lajos/Tantillus/Laser cut case/Panels - 0.25 inch stock/joint/right_b.dxf

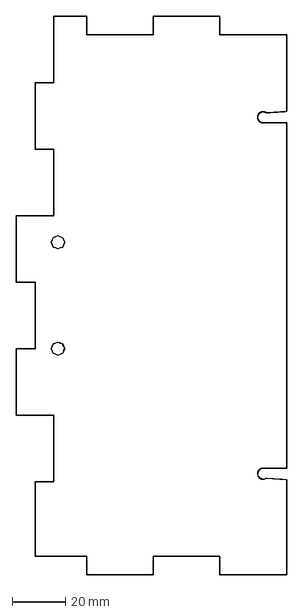
[picture p15: CAD file, 2013-06-04]
Laser cut case/Panels - 0.25 inch stock/joint/right_b.dxf
101.5 x 209.8 mm
