lajos/Tantillus/Laser cut case/Panels - 0.25 inch stock/one piece/front.dxf

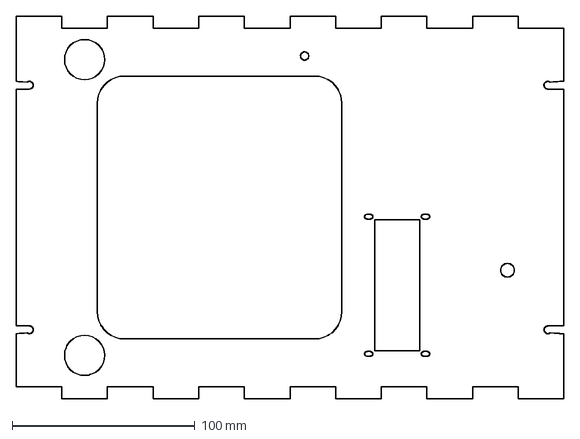
[picture p16: CAD file, 2013-06-04]
Laser cut case/Panels - 0.25 inch stock/one piece/front.dxf
300.0 x 209.8 mm
