lajos/Tantillus/Oilite + Metal Hotend Parts/LED_holder.stl

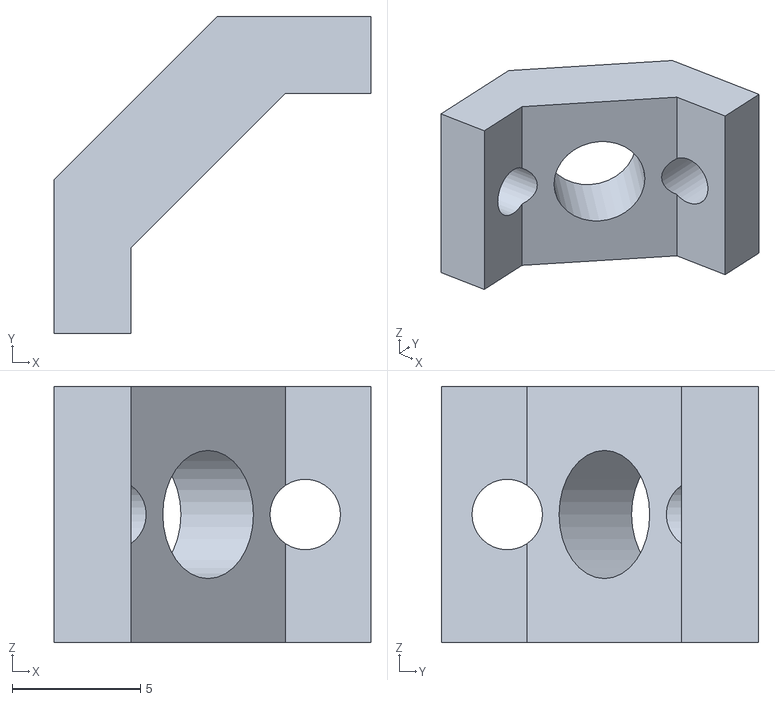
[picture p17: CAD file, 2019-10-04]
Oilite + Metal Hotend Parts/LED_holder.stl
12.4 x 12.4 x 10.0
