lajos/Tantillus/Axis/Oilite/carriage_oilite_bottom.stl

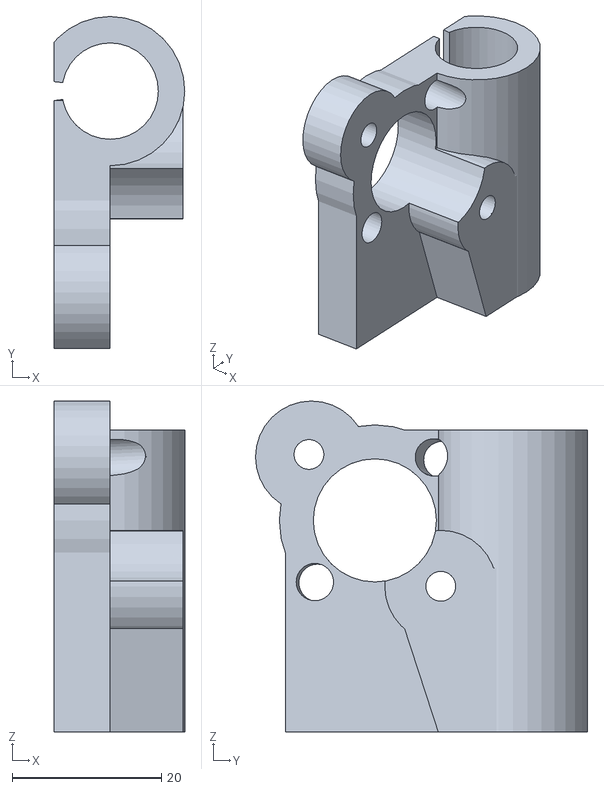
[picture p18: CAD file, 2013-06-04]
Axis/Oilite/carriage_oilite_bottom.stl
17.5 x 44.5 x 44.4
