lajos/Tantillus/Extras/50mm_fanmount_(LC)_0.25_inch_stock.stl

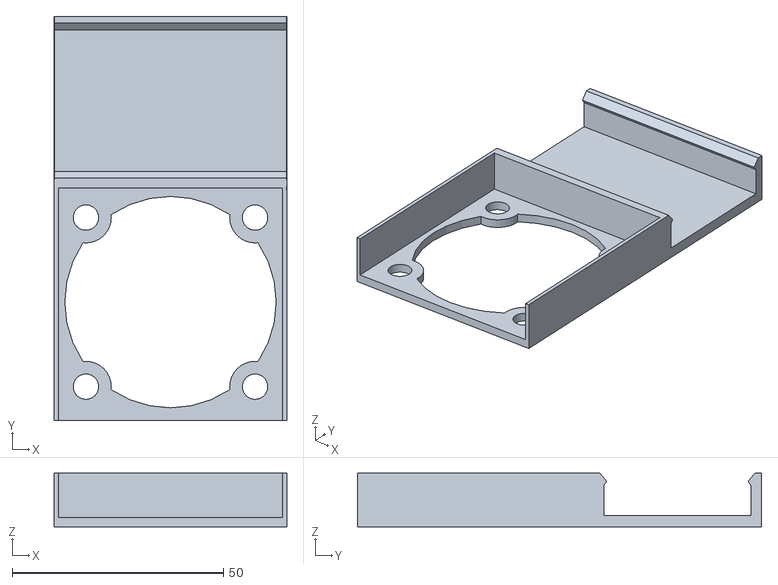
[picture p19: CAD file, 2013-06-04]
Extras/50mm_fanmount_(LC)_0.25_inch_stock.stl
55.0 x 95.6 x 12.7
