lajos/Tantillus/Gears/Spur gears/upper_gear_set.dxf

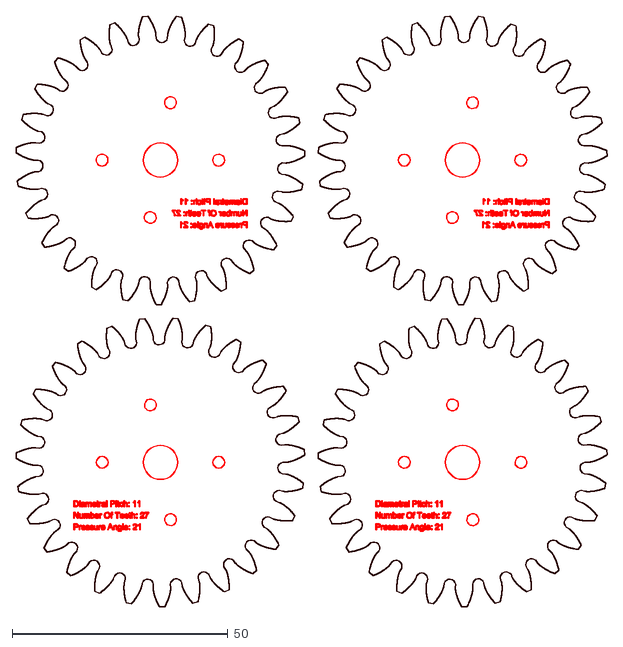
[picture p20: CAD file, 2013-06-05]
Gears/Spur gears/upper_gear_set.dxf
136.9 x 136.8
