lajos/Tantillus/Laser cut case/Corners - 0.25 inch stock/with tabs/corner_top_rear_right.stl

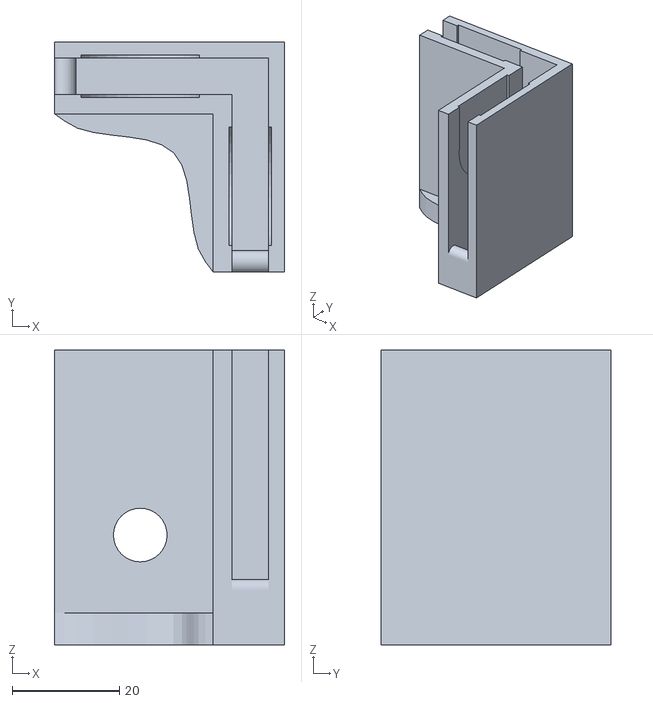
[picture p21: CAD file, 2013-06-04]
Laser cut case/Corners - 0.25 inch stock/with tabs/corner_top_rear_right.stl
42.9 x 42.9 x 55.0
