lajos/Tantillus/Laser cut case/Panels - 0.25 inch stock/joint/right_a.dxf

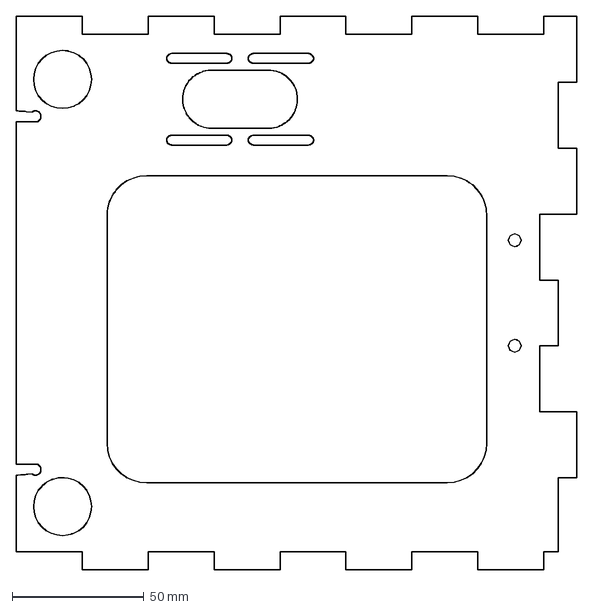
[picture p22: CAD file, 2013-06-04]
Laser cut case/Panels - 0.25 inch stock/joint/right_a.dxf
212.5 x 209.8 mm
