lajos/Tantillus/Oilite + Metal Hotend Parts/xy_slider_b.stl

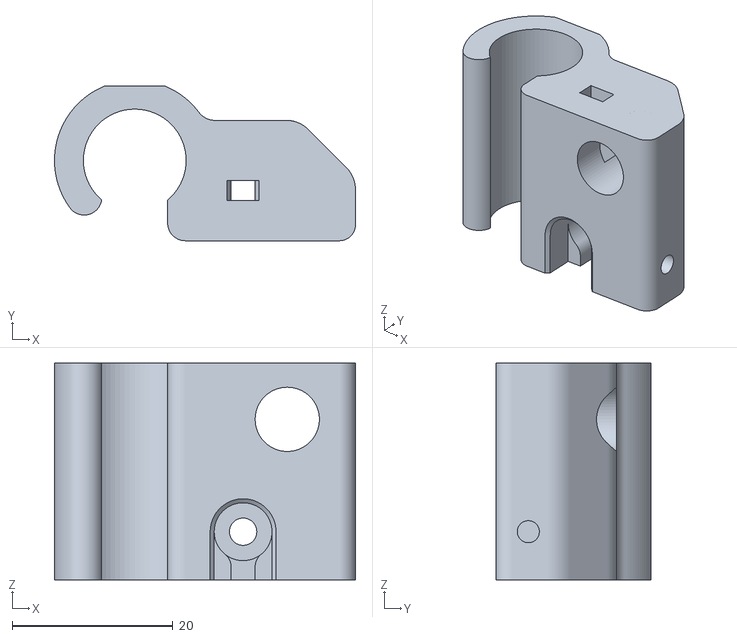
[picture p24: CAD file, 2019-10-03]
Oilite + Metal Hotend Parts/xy_slider_b.stl
37.5 x 19.3 x 27.0
