lajos/Tantillus/Gears/Spur gears/motor_gear.dxf

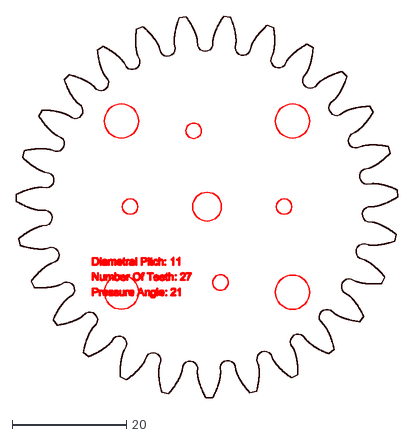
[picture p25: CAD file, 2013-06-05]
Gears/Spur gears/motor_gear.dxf
66.9 x 66.8
