lajos/Tantillus/Laser cut case/Panels - 0.25 inch stock/joint/left_b.dxf

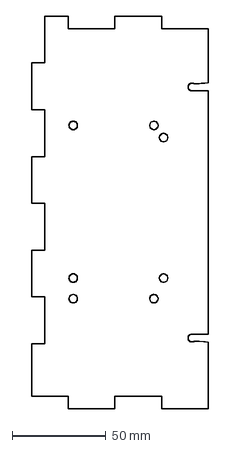
[picture p26: CAD file, 2013-06-04]
Laser cut case/Panels - 0.25 inch stock/joint/left_b.dxf
94.5 x 209.8 mm
