lajos/Tantillus/Oilite + Metal Hotend Parts/spacer_m3_2.stl

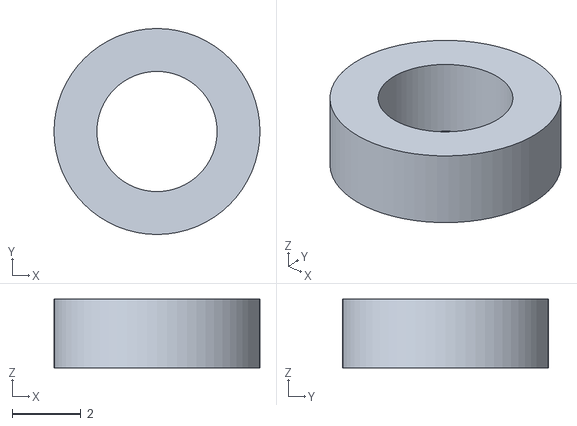
[picture p27: CAD file, 2019-10-03]
Oilite + Metal Hotend Parts/spacer_m3_2.stl
6.00 x 6.00 x 2.00
