lajos/Tantillus/Laser cut case/Panels - 0.25 inch stock/joint/back_a.dxf

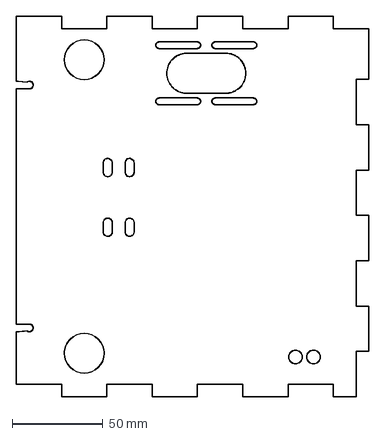
[picture p29: CAD file, 2013-06-04]
Laser cut case/Panels - 0.25 inch stock/joint/back_a.dxf
194.5 x 209.8 mm
