lajos/Tantillus/Oilite + Metal Hotend Parts/spacer_m3_3.stl

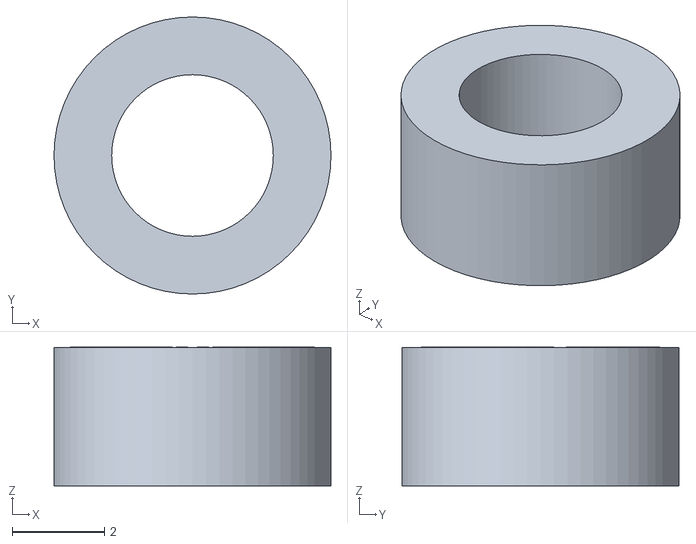
[picture p30: CAD file, 2019-10-03]
Oilite + Metal Hotend Parts/spacer_m3_3.stl
6.00 x 6.00 x 3.00
