lajos/Tantillus/Laser cut case/Panels - 0.25 inch stock/joint/back_b.dxf

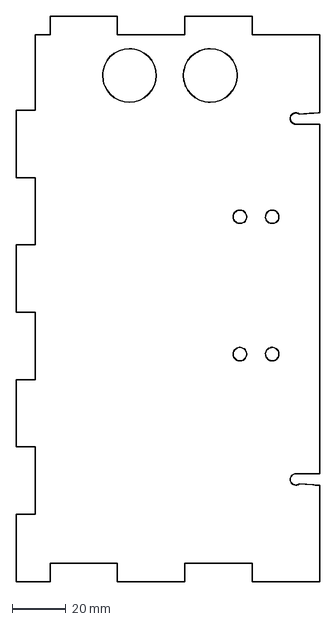
[picture p31: CAD file, 2013-06-04]
Laser cut case/Panels - 0.25 inch stock/joint/back_b.dxf
112.5 x 209.8 mm
