lajos/Tantillus/Oilite + Metal Hotend Parts/z_arm.stl

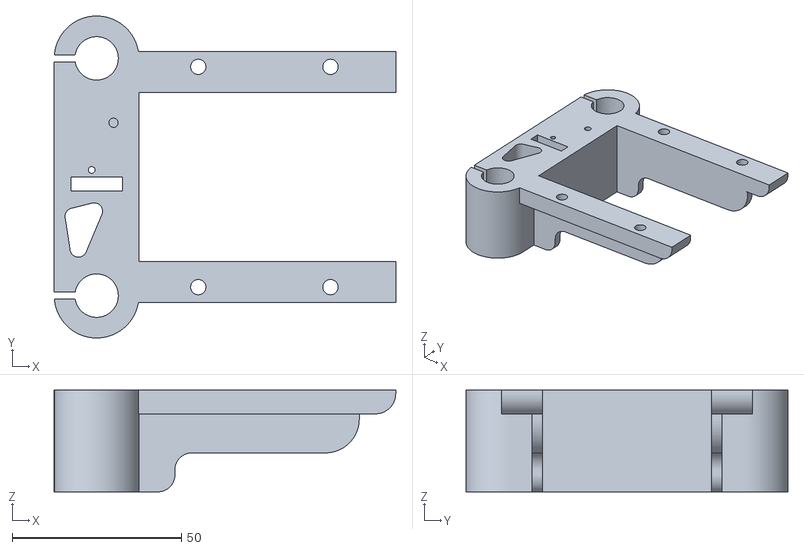
[picture p32: CAD file, 2019-10-03]
Oilite + Metal Hotend Parts/z_arm.stl
100.8 x 95.0 x 30.0
