lajos/Tantillus/Laser cut case/Panels - 0.25 inch stock/joint/front_a.dxf

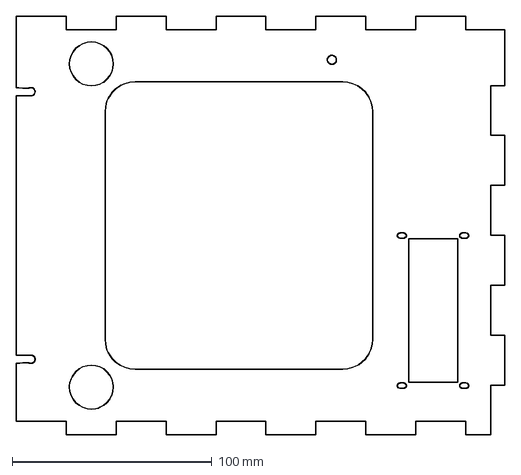
[picture p33: CAD file, 2013-06-04]
Laser cut case/Panels - 0.25 inch stock/joint/front_a.dxf
244.5 x 209.8 mm
