lajos/Tantillus/Laser cut case/Panels - 0.25 inch stock/joint/front_b.dxf

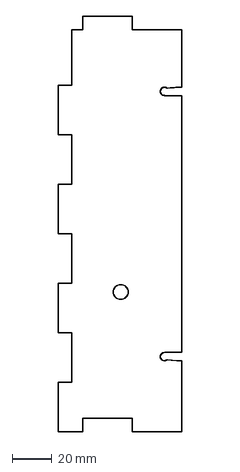
[picture p35: CAD file, 2013-06-04]
Laser cut case/Panels - 0.25 inch stock/joint/front_b.dxf
62.5 x 209.8 mm
