lajos/Tantillus/Oilite + Metal Hotend Parts/z_home_base.stl

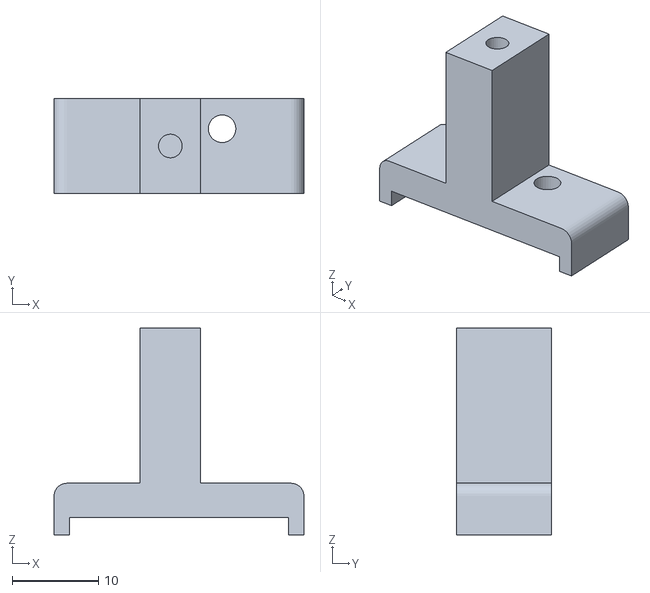
[picture p36: CAD file, 2019-10-03]
Oilite + Metal Hotend Parts/z_home_base.stl
29.0 x 11.0 x 24.0
