lajos/Tantillus/Gears/Spur gears/upper_gear_half.dxf

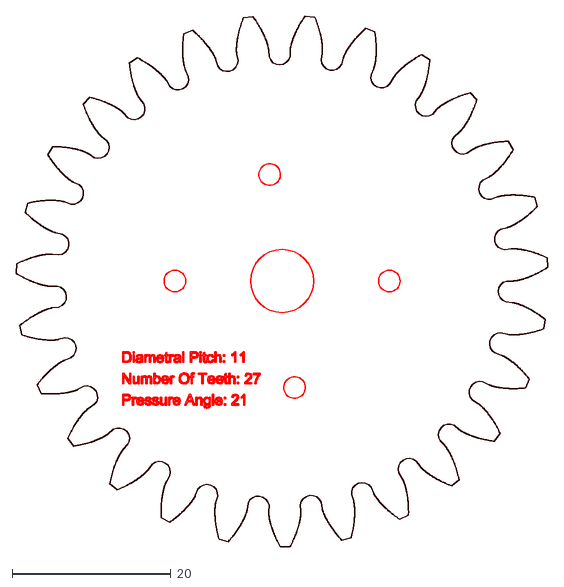
[picture p37: CAD file, 2013-06-04]
Gears/Spur gears/upper_gear_half.dxf
66.9 x 66.8
