lajos/Tantillus/Oilite + Metal Hotend Parts/spacer_m3_5.stl

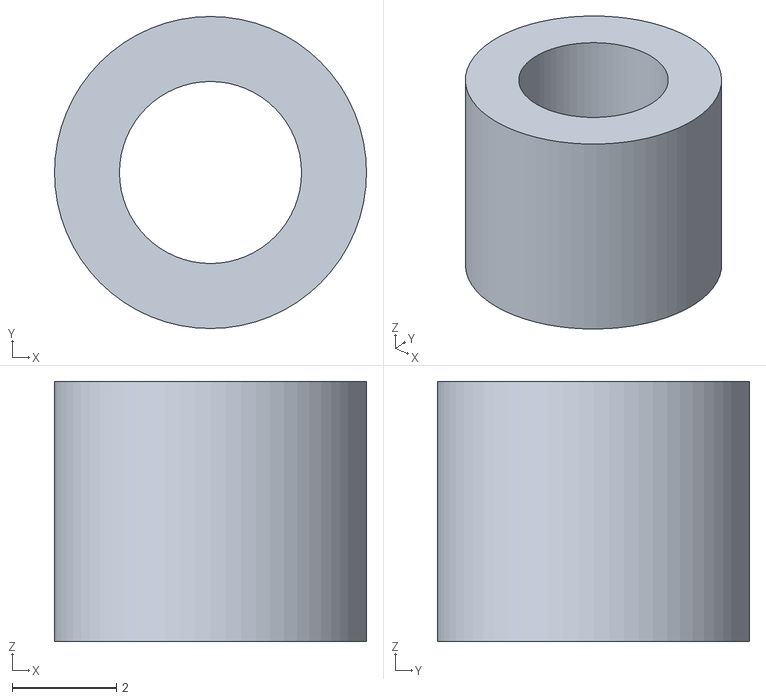
[picture p38: CAD file, 2019-10-03]
Oilite + Metal Hotend Parts/spacer_m3_5.stl
6.00 x 6.00 x 5.00
