lajos/Tantillus/Oilite + Metal Hotend Parts/fan_mount_lower.stl

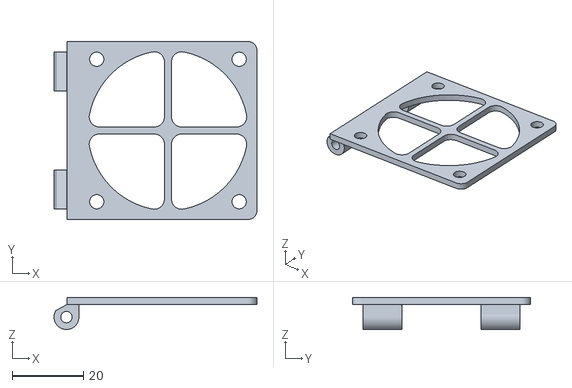
[picture p39: CAD file, 2019-10-03]
Oilite + Metal Hotend Parts/fan_mount_lower.stl
57.0 x 50.0 x 9.01
