lajos/Tantillus/Oilite + Metal Hotend Parts/z_upper.stl

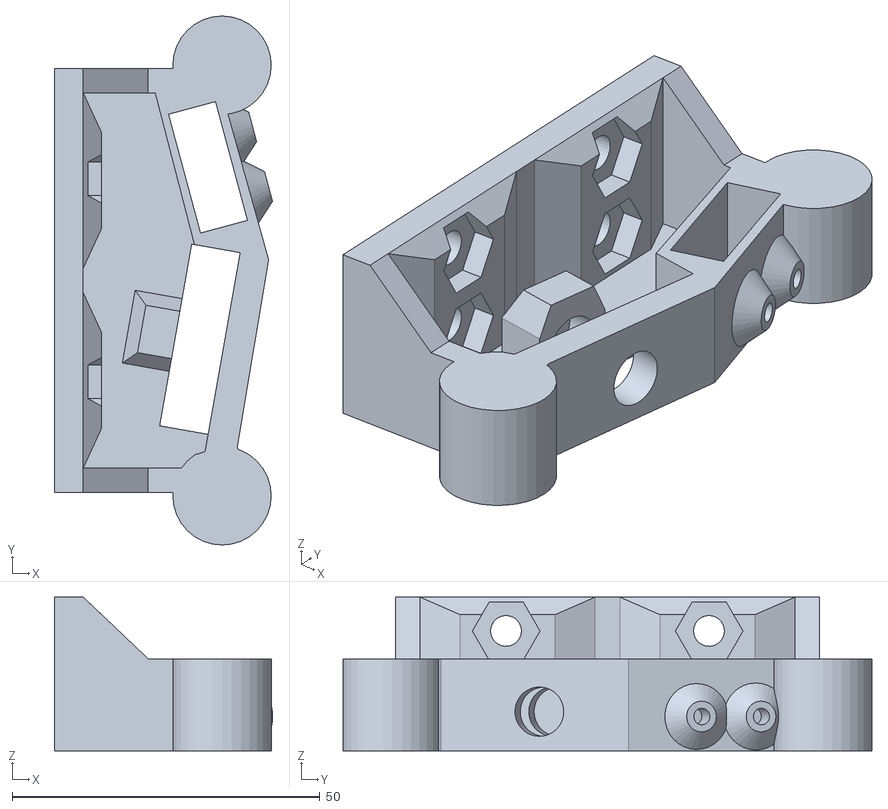
[picture p40: CAD file, 2019-10-03]
Oilite + Metal Hotend Parts/z_upper.stl
35.5 x 86.0 x 25.0
