lajos/Tantillus/Oilite + Metal Hotend Parts/corner_top_rear_left.stl

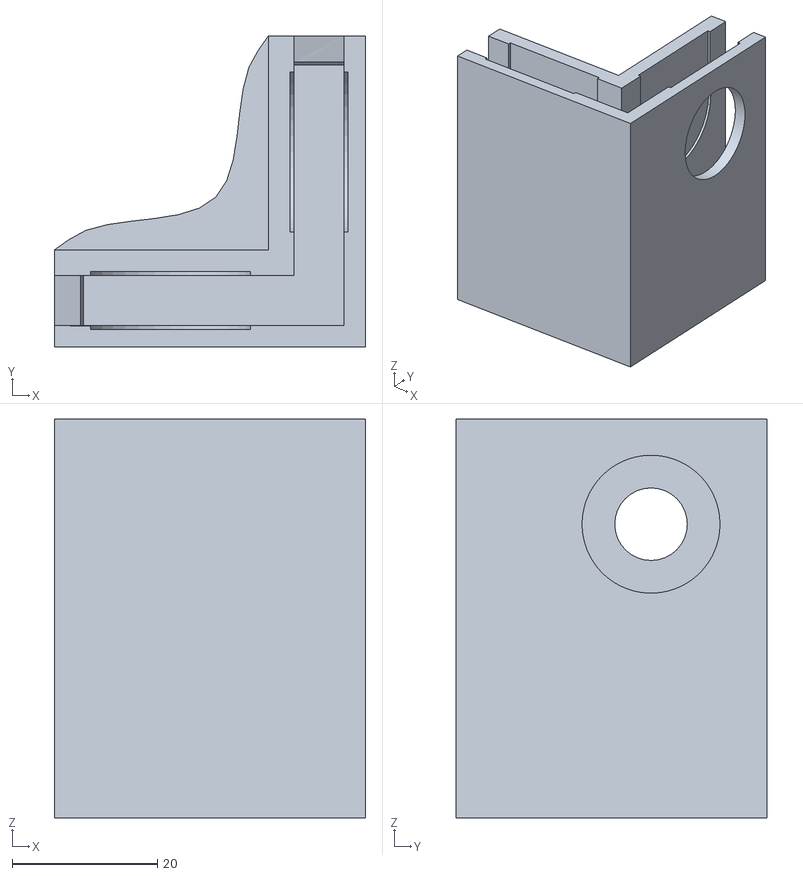
[picture p41: CAD file, 2019-10-03]
Oilite + Metal Hotend Parts/corner_top_rear_left.stl
42.9 x 42.9 x 55.0
