lajos/Tantillus/Oilite + Metal Hotend Parts/z_spacer_short.stl

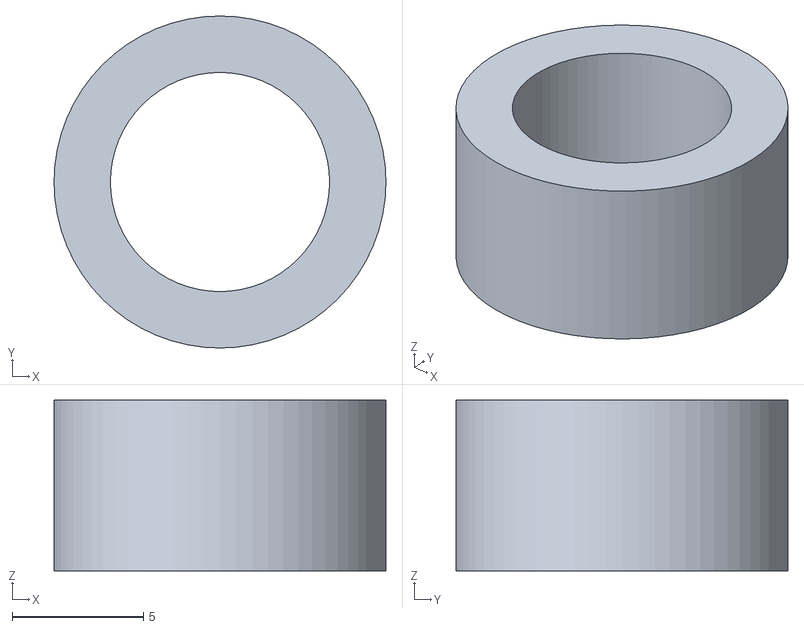
[picture p42: CAD file, 2019-10-03]
Oilite + Metal Hotend Parts/z_spacer_short.stl
12.6 x 12.6 x 6.50
