lajos/Tantillus/Oilite + Metal Hotend Parts/z_upper_idler.stl

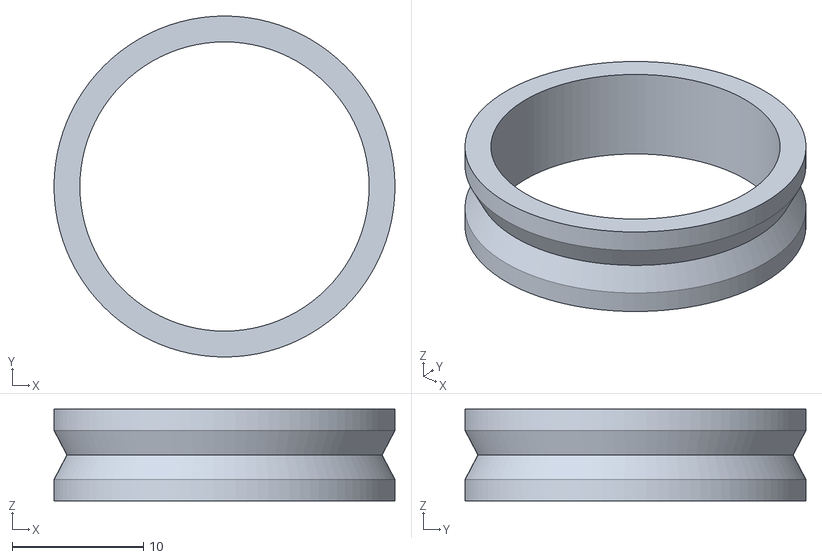
[picture p43: CAD file, 2019-10-03]
Oilite + Metal Hotend Parts/z_upper_idler.stl
26.0 x 26.0 x 7.00
