lajos/Tantillus/Oilite + Metal Hotend Parts/z_tensioner.stl

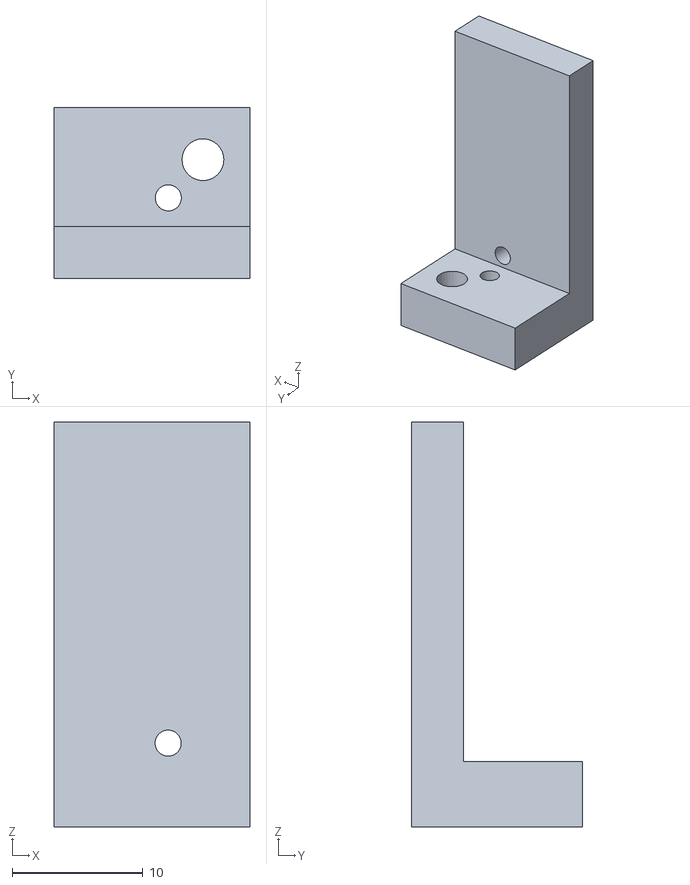
[picture p44: CAD file, 2019-10-03]
Oilite + Metal Hotend Parts/z_tensioner.stl
15.0 x 13.1 x 31.0
