lajos/Tantillus/Oilite + Metal Hotend Parts/extruder_motor_spacer.stl

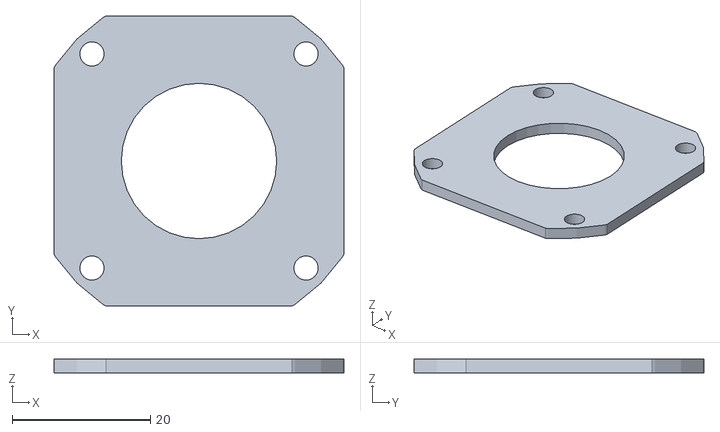
[picture p45: CAD file, 2019-10-03]
Oilite + Metal Hotend Parts/extruder_motor_spacer.stl
42.0 x 42.0 x 2.00
