lajos/Tantillus/Oilite + Metal Hotend Parts/z_lift.stl

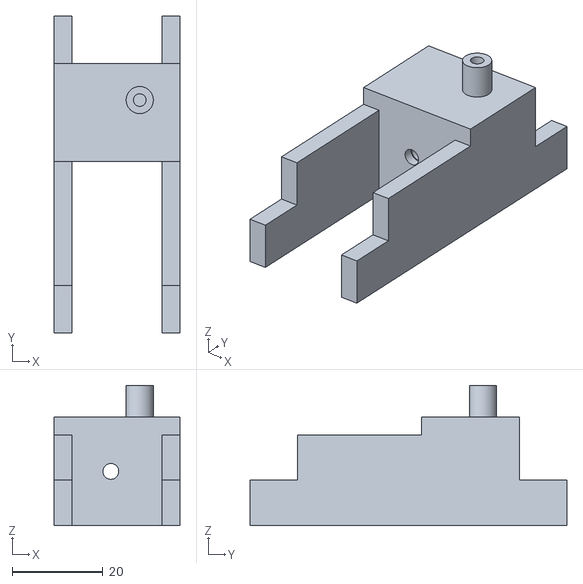
[picture p46: CAD file, 2019-10-03]
Oilite + Metal Hotend Parts/z_lift.stl
27.8 x 70.0 x 30.9
