lajos/Tantillus/Oilite + Metal Hotend Parts/xy_carriage_middle.stl

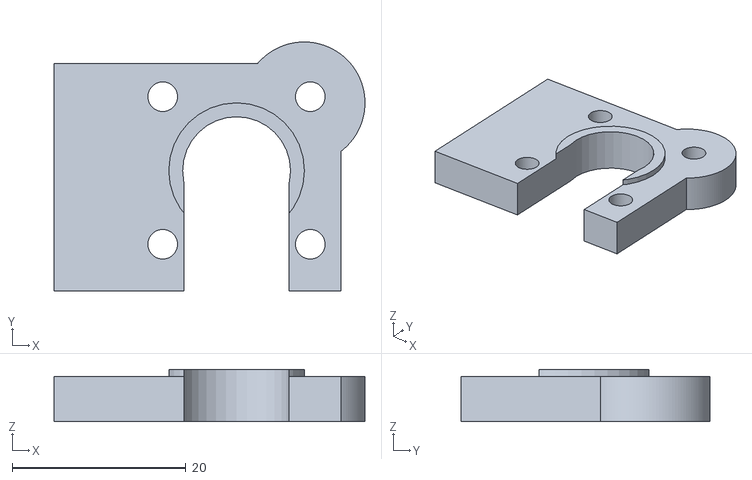
[picture p47: CAD file, 2019-10-03]
Oilite + Metal Hotend Parts/xy_carriage_middle.stl
35.8 x 28.6 x 6.00
