lajos/Tantillus/Oilite + Metal Hotend Parts/z_lower.stl

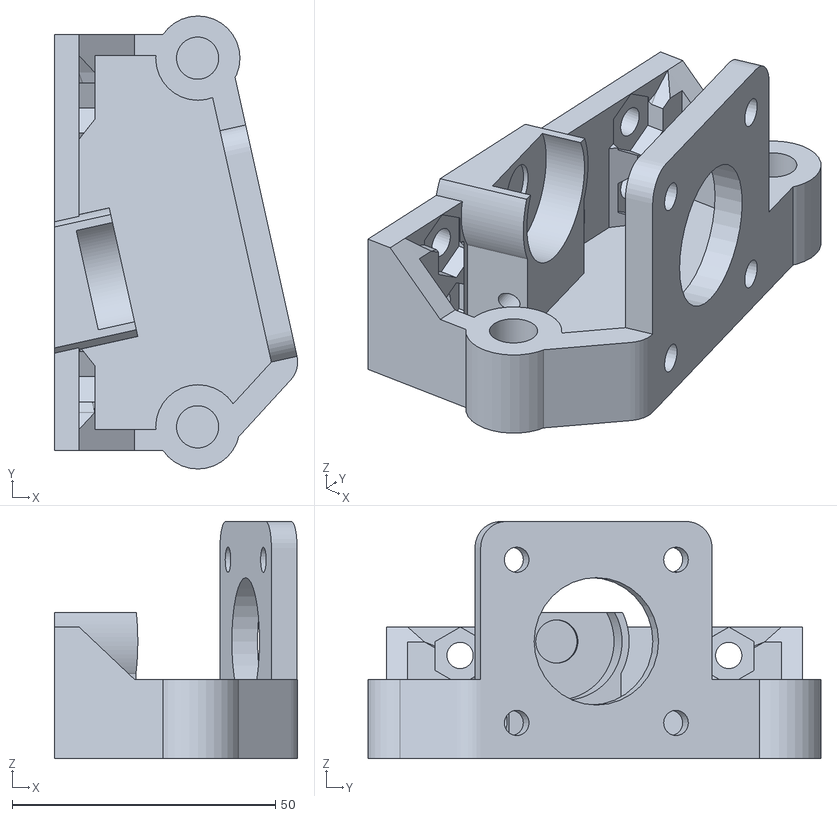
[picture p49: CAD file, 2019-10-03]
Oilite + Metal Hotend Parts/z_lower.stl
46.2 x 86.0 x 45.0
