lajos/Tantillus/Oilite + Metal Hotend Parts/z_upper_t8.stl

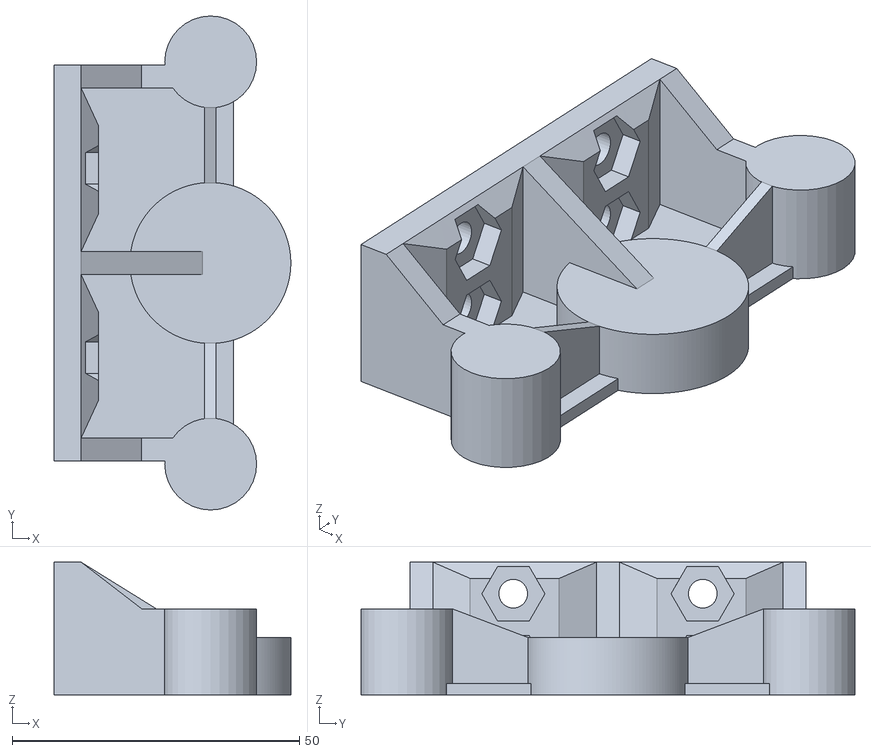
[picture p50: CAD file, 2019-10-03]
Oilite + Metal Hotend Parts/z_upper_t8.stl
41.2 x 86.0 x 23.1
