lajos/Tantillus/Oilite + Metal Hotend Parts/xy_carriage_bottom.stl

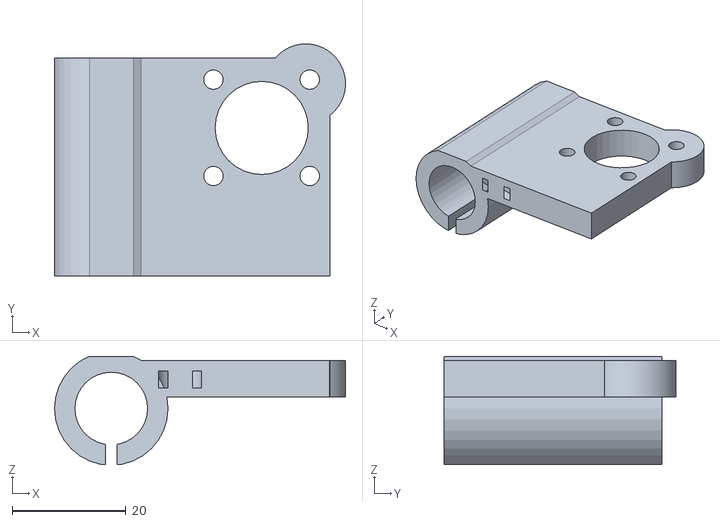
[picture p51: CAD file, 2019-10-03]
Oilite + Metal Hotend Parts/xy_carriage_bottom.stl
51.3 x 40.9 x 19.1
