lajos/Tantillus/Oilite + Metal Hotend Parts/spacer_m3_4.stl

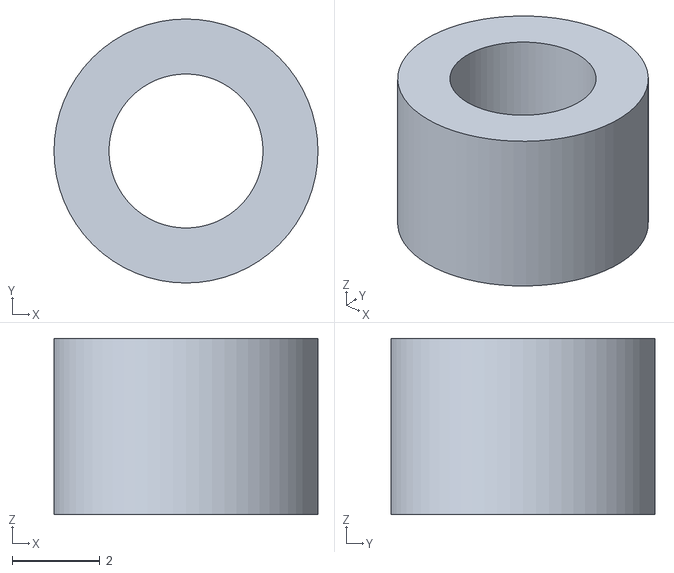
[picture p52: CAD file, 2019-10-03]
Oilite + Metal Hotend Parts/spacer_m3_4.stl
6.00 x 6.00 x 4.00
