lajos/Tantillus/Oilite + Metal Hotend Parts/z_endstop_mount_9.5.stl

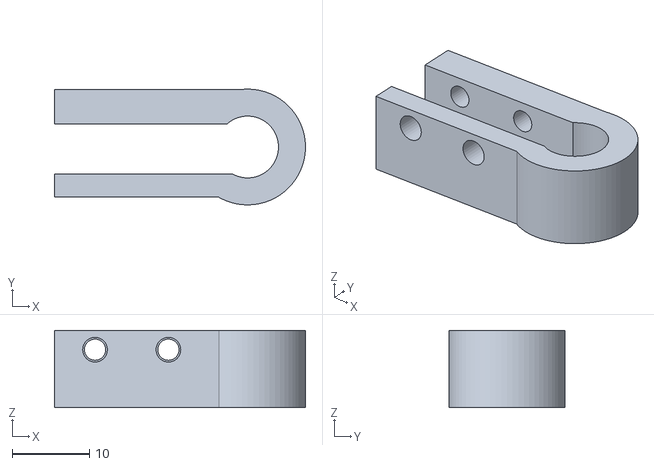
[picture p53: CAD file, 2019-10-03]
Oilite + Metal Hotend Parts/z_endstop_mount_9.5.stl
32.5 x 15.0 x 10.0
