lajos/Tantillus/Oilite + Metal Hotend Parts/z_arm_t8.stl

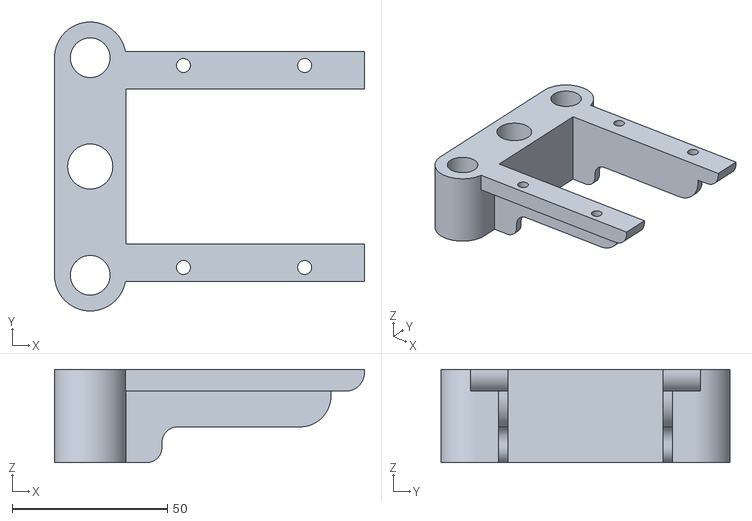
[picture p54: CAD file, 2019-10-03]
Oilite + Metal Hotend Parts/z_arm_t8.stl
99.8 x 93.0 x 30.0
