lajos/Tantillus/Oilite + Metal Hotend Parts/z_arm_t8_plate.stl

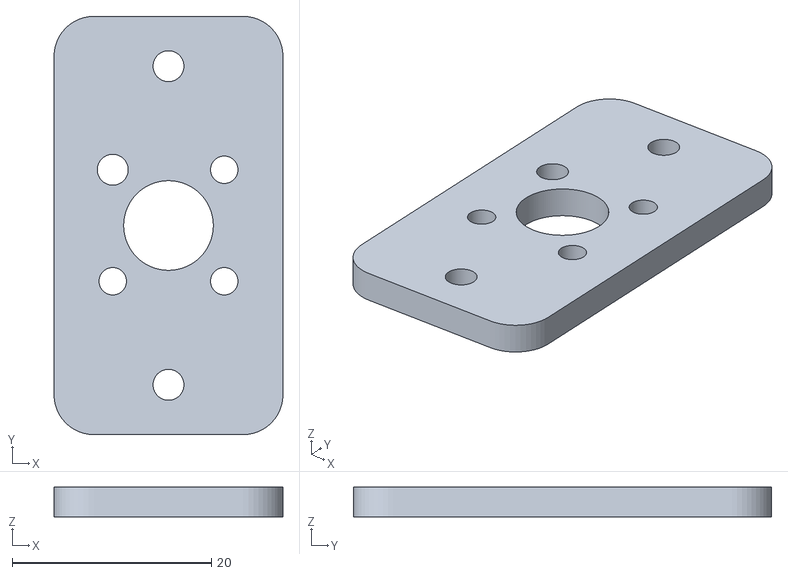
[picture p55: CAD file, 2019-10-03]
Oilite + Metal Hotend Parts/z_arm_t8_plate.stl
23.0 x 42.0 x 3.00
