lajos/Tantillus/Oilite + Metal Hotend Parts/fan_mount_upper.stl

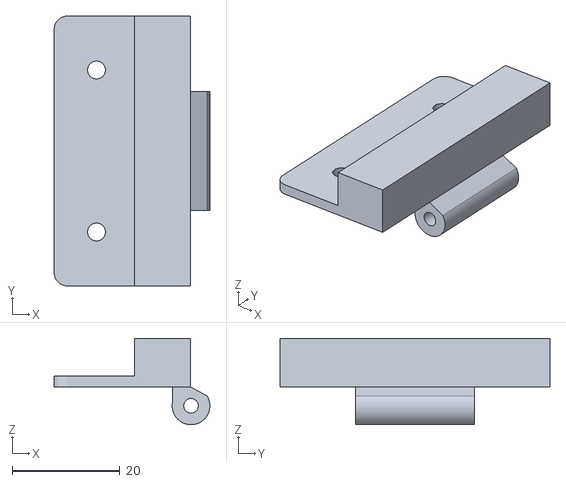
[picture p56: CAD file, 2019-10-03]
Oilite + Metal Hotend Parts/fan_mount_upper.stl
28.9 x 50.0 x 16.0
