lajos/Tantillus/Oilite + Metal Hotend Parts/xy_carriage_top.stl

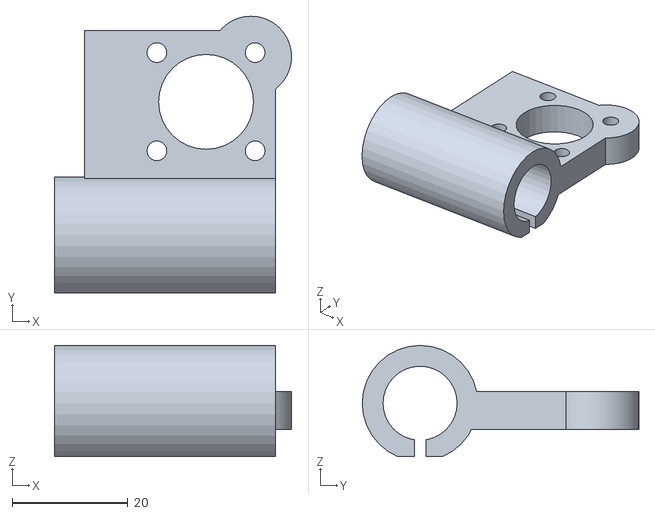
[picture p57: CAD file, 2019-10-03]
Oilite + Metal Hotend Parts/xy_carriage_top.stl
41.0 x 47.8 x 19.2
