lajos/Tantillus/Oilite + Metal Hotend Parts/z_motor_mount_t8.stl

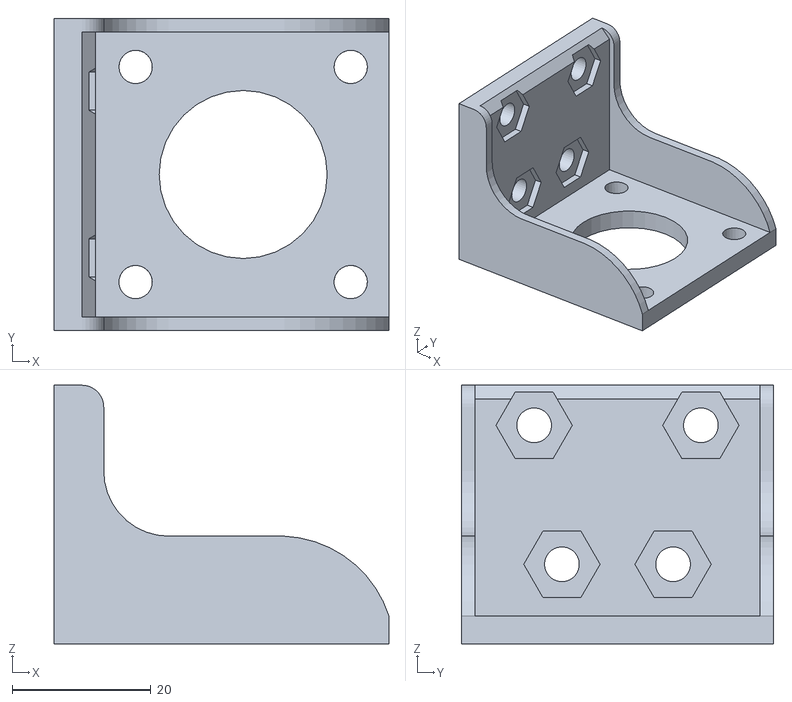
[picture p58: CAD file, 2019-10-03]
Oilite + Metal Hotend Parts/z_motor_mount_t8.stl
48.2 x 45.0 x 37.2
