lajos/Tantillus/Oilite + Metal Hotend Parts/z_home_knob_bottom.stl

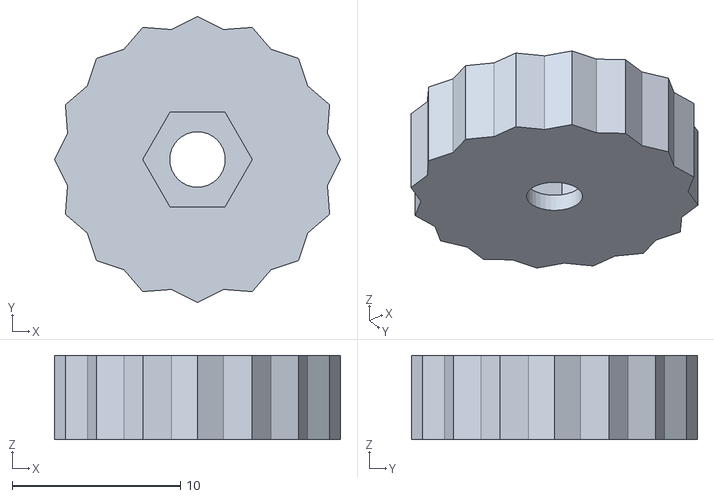
[picture p59: CAD file, 2019-10-03]
Oilite + Metal Hotend Parts/z_home_knob_bottom.stl
17.0 x 17.0 x 5.00
