lajos/Tantillus/Oilite + Metal Hotend Parts/power_connector_mount.stl

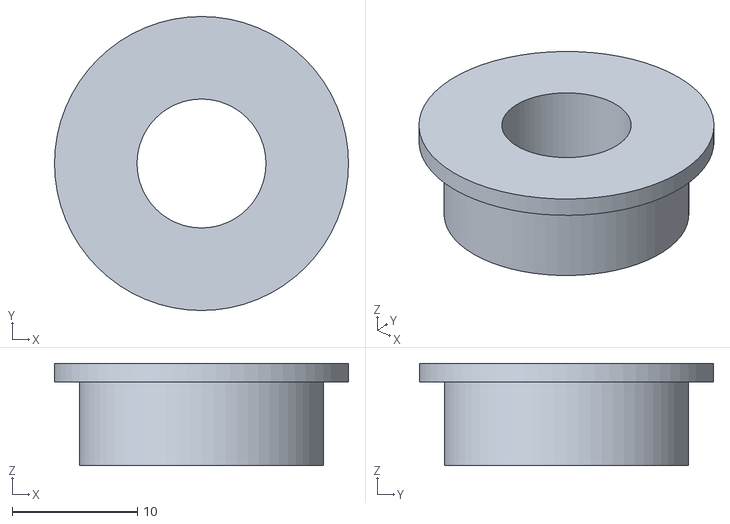
[picture p60: CAD file, 2019-10-03]
Oilite + Metal Hotend Parts/power_connector_mount.stl
23.5 x 23.5 x 8.19
