lajos/Tantillus/Oilite + Metal Hotend Parts/z_drum.stl

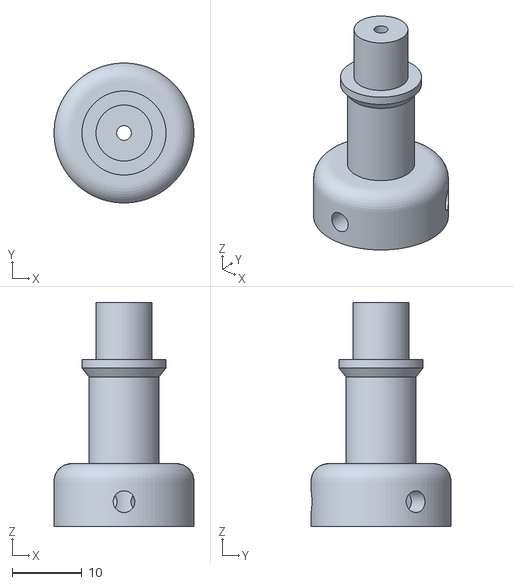
[picture p61: CAD file, 2019-10-03]
Oilite + Metal Hotend Parts/z_drum.stl
20.0 x 20.0 x 32.0
