lajos/Tantillus/Oilite + Metal Hotend Parts/rotary_knob.stl

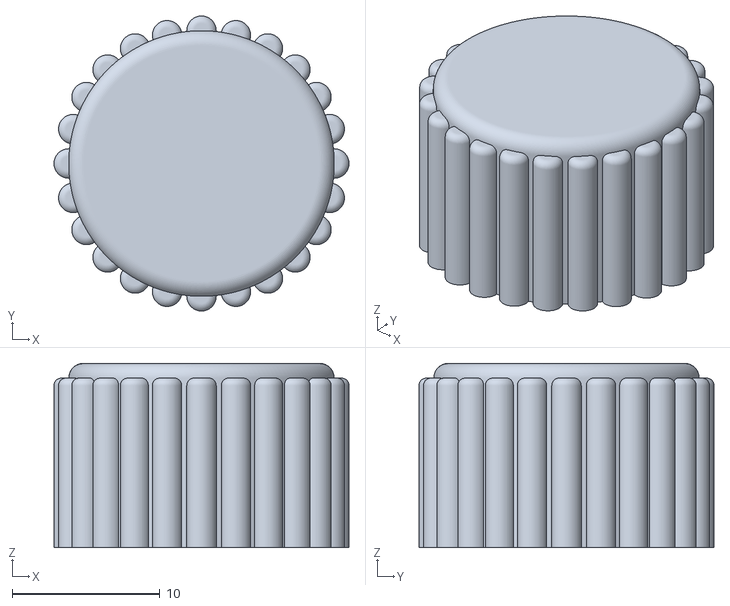
[picture p62: CAD file, 2019-10-03]
Oilite + Metal Hotend Parts/rotary_knob.stl
20.0 x 20.0 x 12.5
