lajos/Tantillus/Oilite + Metal Hotend Parts/fan_nozzle.stl

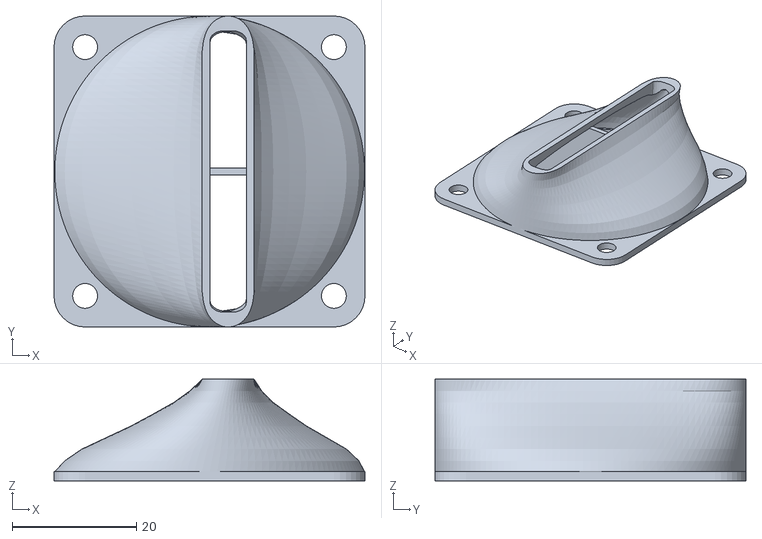
[picture p63: CAD file, 2019-10-03]
Oilite + Metal Hotend Parts/fan_nozzle.stl
50.0 x 50.0 x 16.4
