lajos/Tantillus/Oilite + Metal Hotend Parts/z_endstop_mount.stl

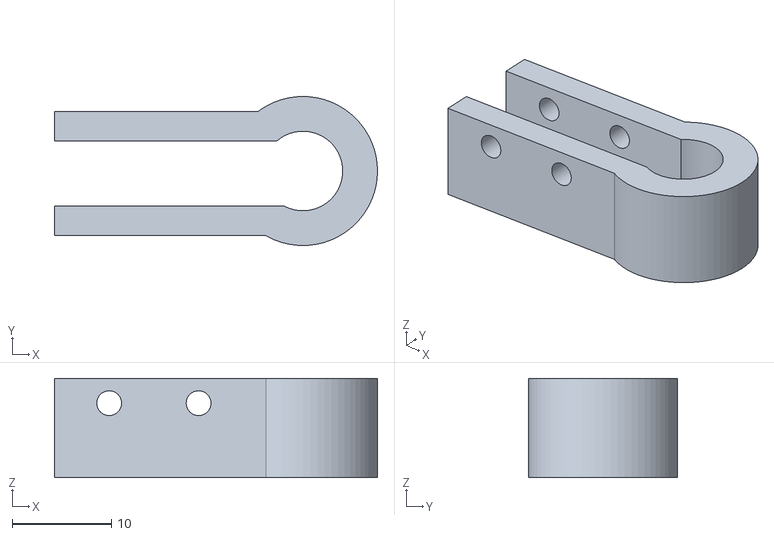
[picture p64: CAD file, 2019-10-03]
Oilite + Metal Hotend Parts/z_endstop_mount.stl
32.5 x 15.0 x 10.0
