lajos/Tantillus/Oilite + Metal Hotend Parts/z_lower_t8.stl

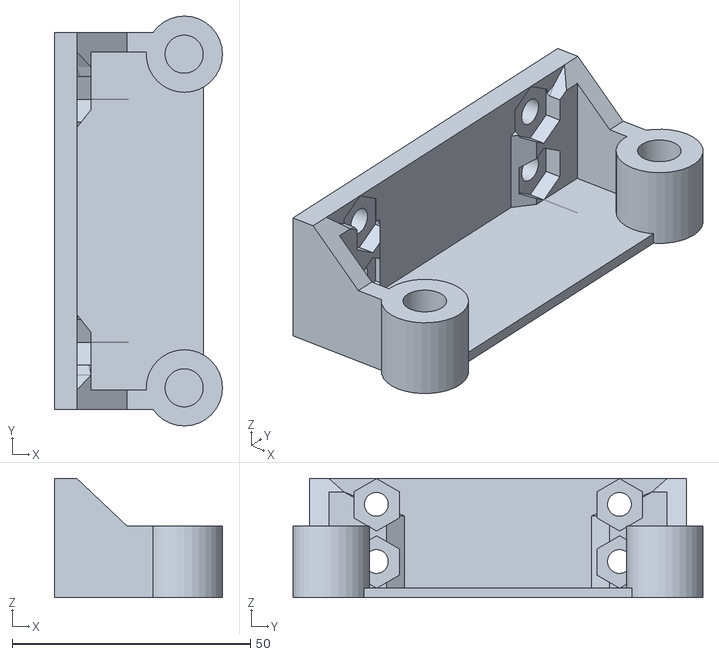
[picture p65: CAD file, 2019-10-03]
Oilite + Metal Hotend Parts/z_lower_t8.stl
35.2 x 86.0 x 25.0
