lajos/Tantillus/Oilite + Metal Hotend Parts/z_spacer_long.stl

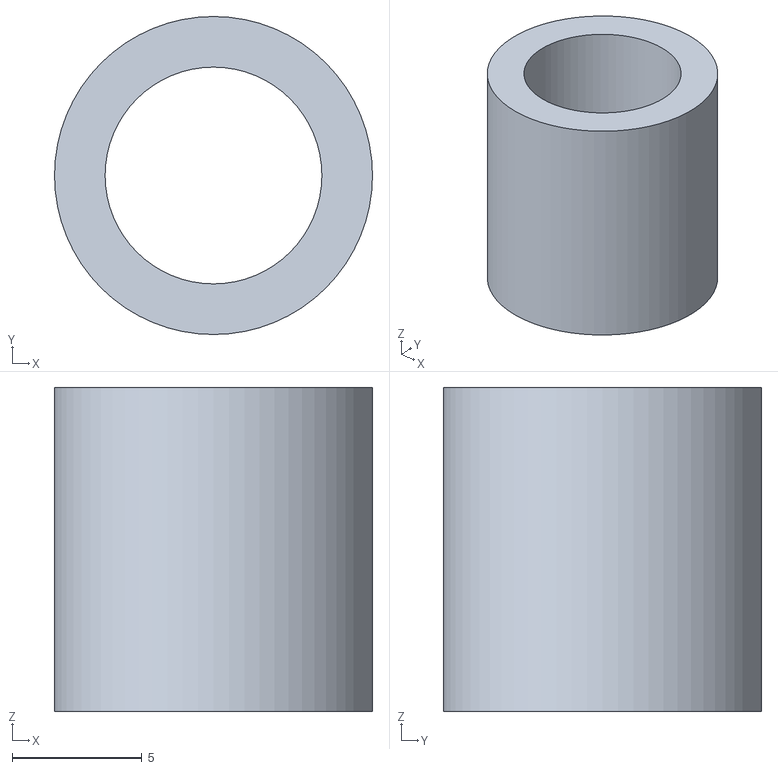
[picture p66: CAD file, 2019-10-03]
Oilite + Metal Hotend Parts/z_spacer_long.stl
12.2 x 12.2 x 12.5
