lajos/Tantillus/Oilite + Metal Hotend Parts/corner_bottom.stl

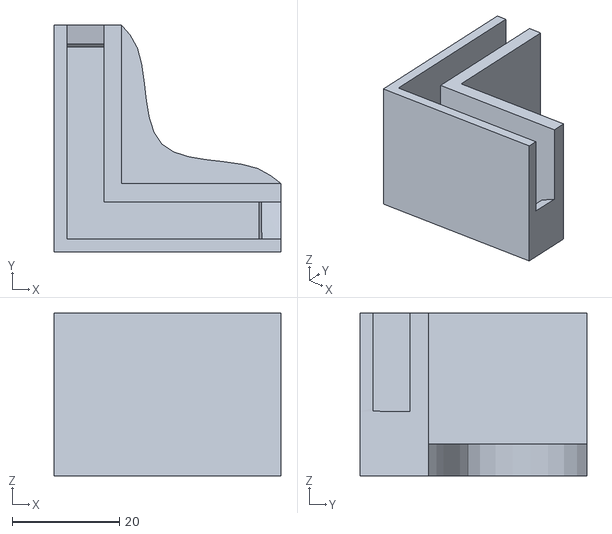
[picture p67: CAD file, 2013-06-04]
Oilite + Metal Hotend Parts/corner_bottom.stl
42.4 x 42.4 x 30.4
