lajos/Tantillus/Oilite + Metal Hotend Parts/z_arm_left.stl

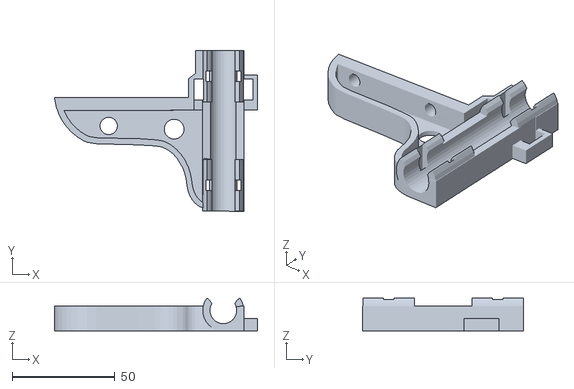
[picture p68: CAD file, 2013-06-04]
Oilite + Metal Hotend Parts/z_arm_left.stl
98.6 x 78.3 x 16.0
