lajos/Tantillus/Oilite + Metal Hotend Parts/z_arm_spacer_small.stl

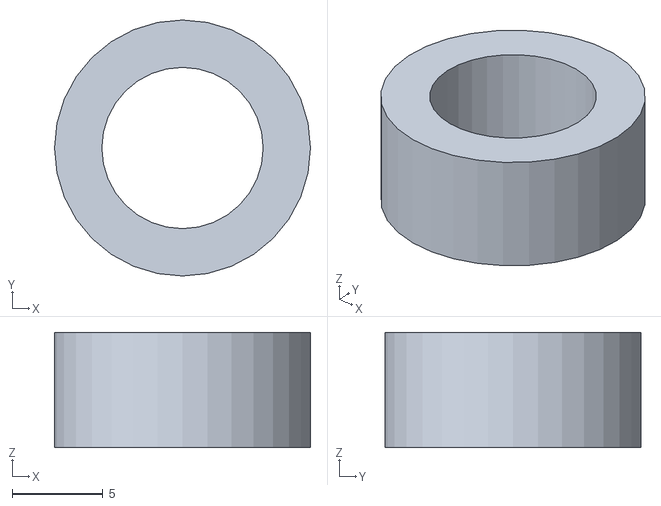
[picture p69: CAD file, 2013-06-04]
Oilite + Metal Hotend Parts/z_arm_spacer_small.stl
14.1 x 14.1 x 6.35
